mikegoelzer/ESP32-Remote-USB-HID/esp32-firmware/arduino-esp32-remote-kybd/esp32-remote-kybd/secrets.h

const char *ssid = "Deer John";                    // change this to your WiFi SSID
const char *password = "orphan&wetsuit-66912406";  // change this to your WiFi password

const char *LOGIN_PASSWORD = "mike";
